Pauliomono/Lightsaber/handle.SLDPRT

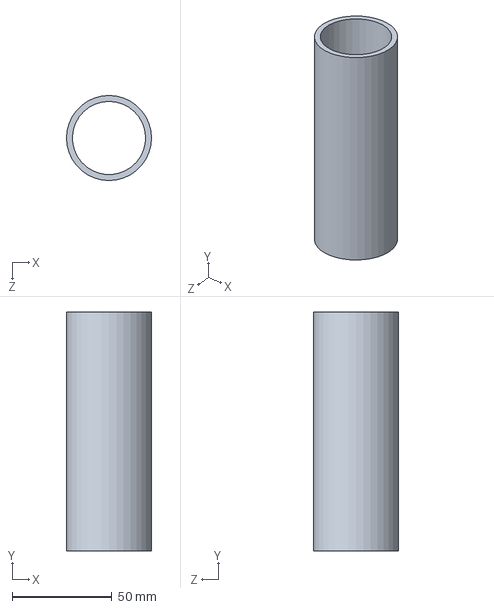
[picture p16: CAD file, 2022-06-29]
handle.SLDPRT
42.7 x 120.0 x 42.7 mm
