Pauliomono/Lightsaber/speaker_housing.SLDPRT

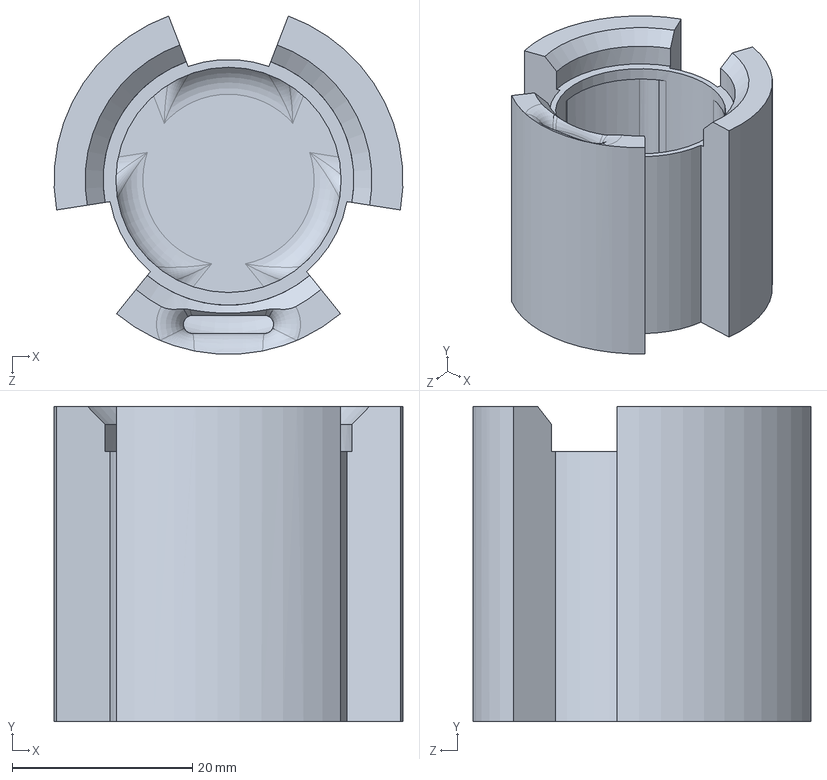
[picture p17: CAD file, 2022-06-29]
speaker_housing.SLDPRT
38.7 x 35.0 x 37.5 mm
