Pauliomono/Lightsaber/button.SLDPRT

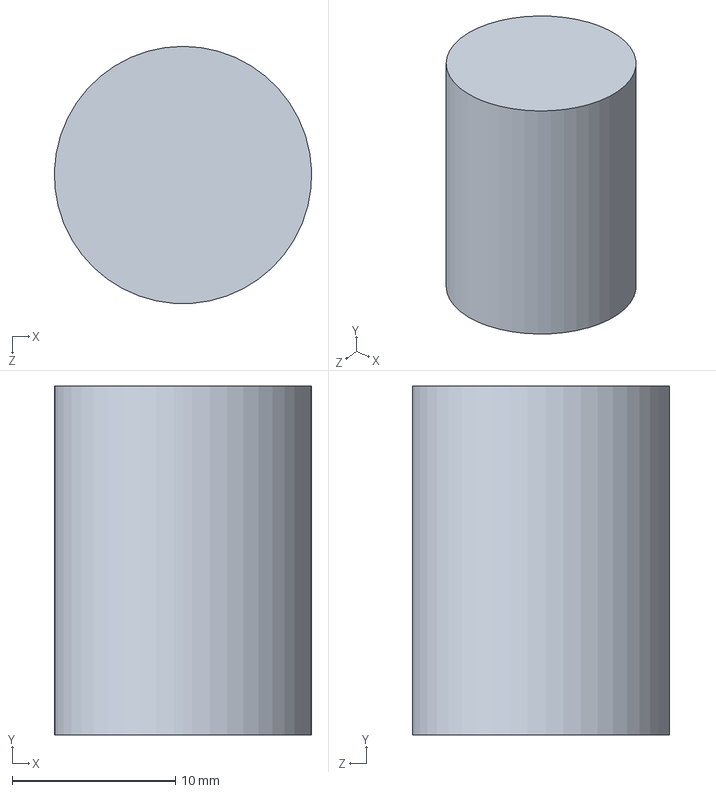
[picture p18: CAD file, 2022-06-29]
button.SLDPRT
15.8 x 21.4 x 15.8 mm
